SteveRMann/garden/history.ino

/*
   History:
   -- Version 1.0 --
   5/23/20 - Forked from GardenProject.  Removed sleep
   -- Version 1.1 --
   5/25/20 - Using ArduinoJson.h to send the data as a JSON string
   -- Version 2.0 --
   5/25/20 - Added separate topics for each item. Home Assistant doesn't handle JSON strings well.

   
*/
